t-dsp/t-dsp_tac5212_pro_audio_module/3d_models/SK6812.step

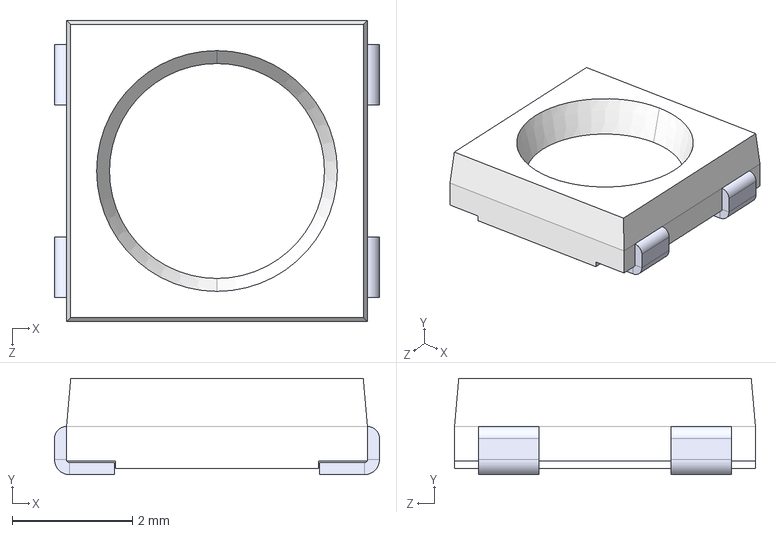
[picture p26: CAD file, 2025-04-21]
3d_models/SK6812.step
5.40 x 1.60 x 5.00 mm
