t-dsp/t-dsp_tac5212_pro_audio_module/3d_models/Same_Sky_SJ3-35083D-TR.step

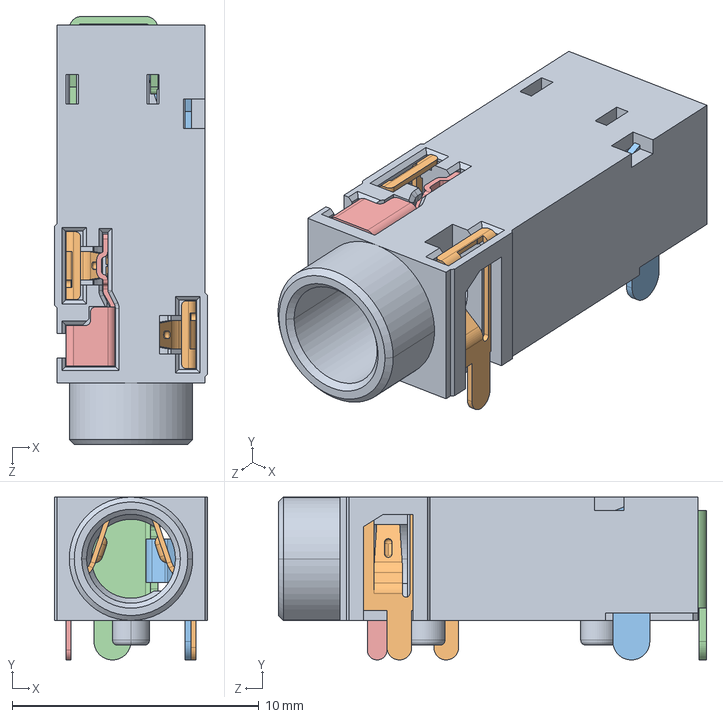
[picture p27: CAD file, 2025-04-21]
3d_models/Same_Sky_SJ3-35083D-TR.step
6.20 x 6.60 x 17.3 mm
