t-dsp/t-dsp_tac5212_pro_audio_module/3d_models/PEC12R-2220F-S0024.step

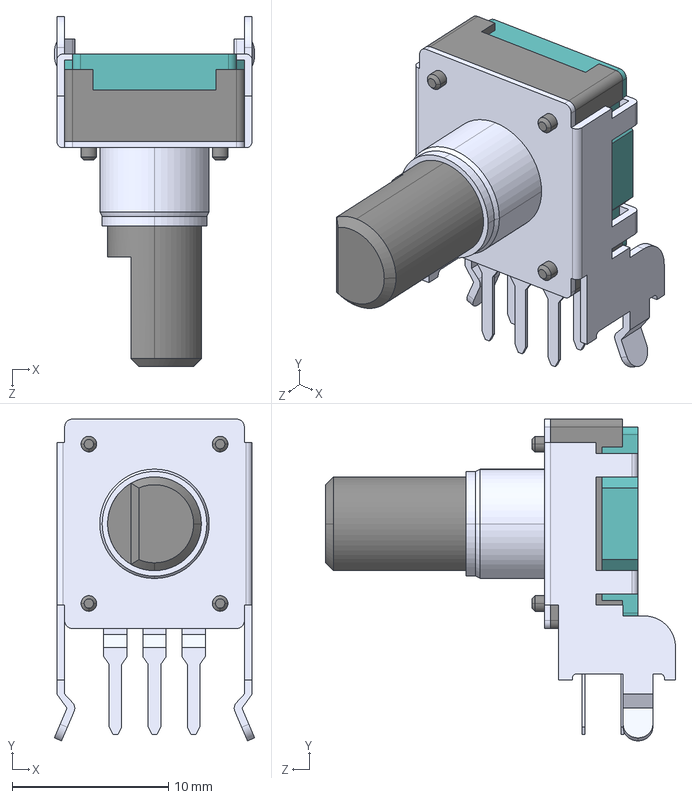
[picture p29: CAD file, 2025-04-21]
3d_models/PEC12R-2220F-S0024.step
12.8 x 20.6 x 22.4 mm
