t-dsp/t-dsp_tac5212_pro_audio_module/3d_models/Tactile_Switch_4.54.5MM.stp

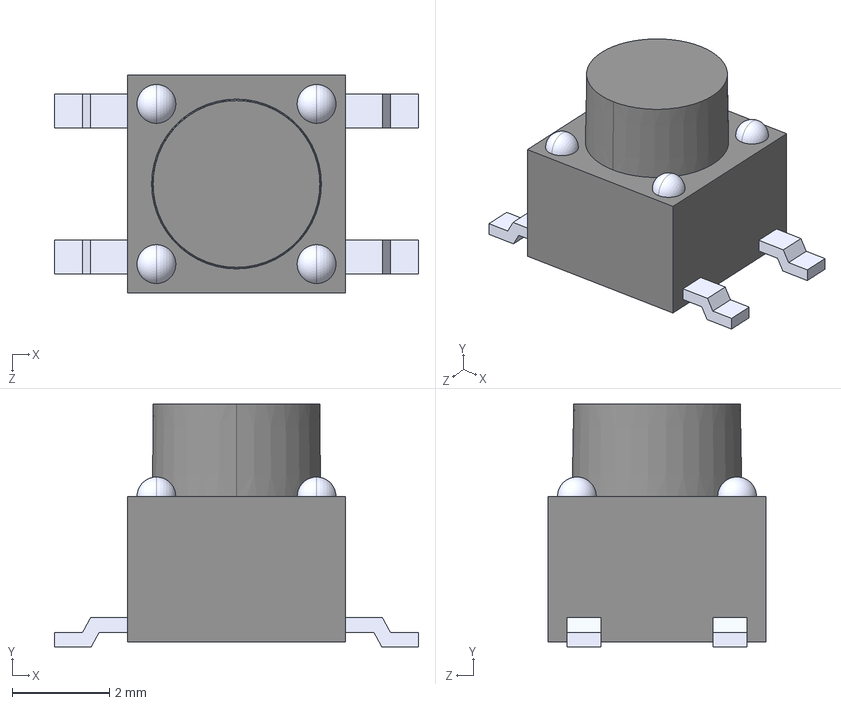
[picture p30: CAD file, 2025-04-21]
3d_models/Tactile_Switch_4.54.5MM.stp
7.50 x 5.00 x 4.50 mm
