t-dsp/t-dsp_tac5212_pro_audio_module/3d_models/JST - XH - Thru (V) - 2Pin - 2.54mm.stp

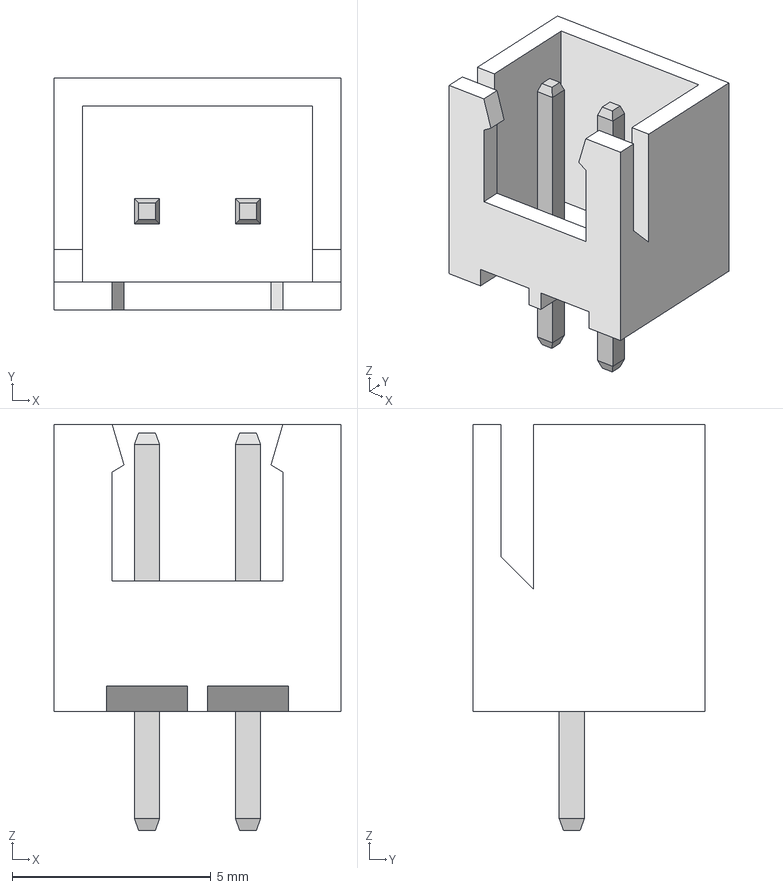
[picture p32: CAD file, 2024-03-24]
3d_models/JST - XH - Thru (V) - 2Pin - 2.54mm.stp
7.21 x 5.84 x 10.2 mm
