t-dsp/t-dsp_tac5212_pro_audio_module/3d_models/4691.step

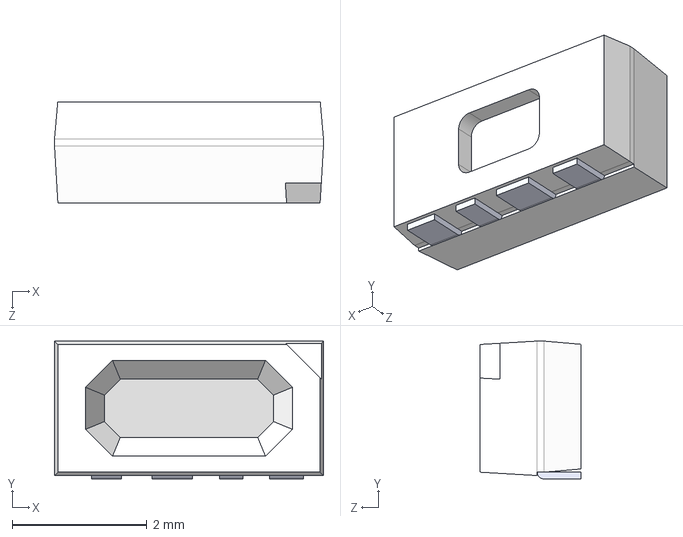
[picture p33: CAD file, 2024-03-24]
3d_models/4691.step
4.00 x 2.05 x 1.50 mm
