t-dsp/t-dsp_tac5212_pro_audio_module/3d_models/1808--3DModel-STEP-630548.STEP

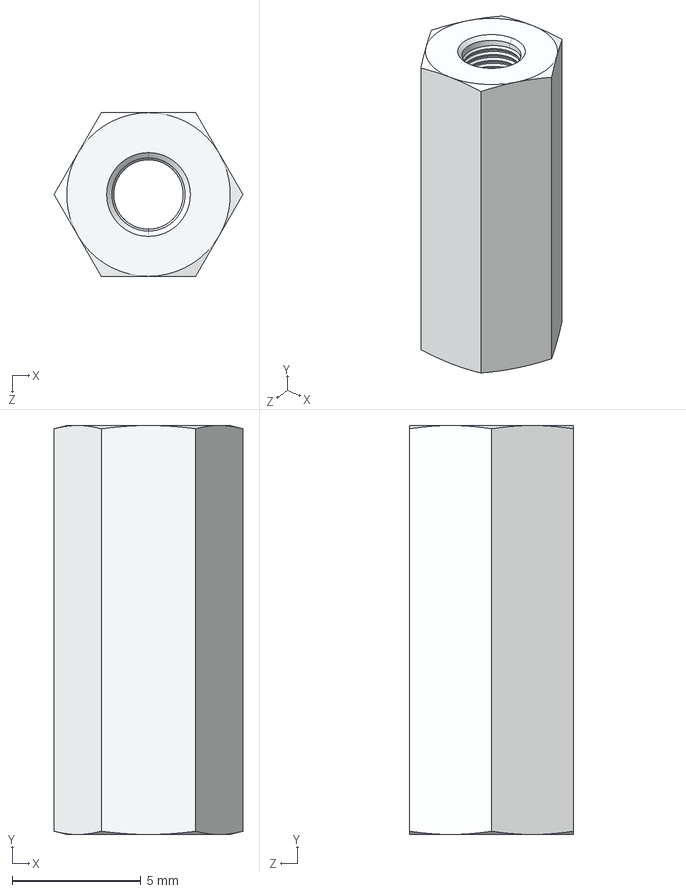
[picture p36: CAD file, 2024-03-16]
3d_models/1808--3DModel-STEP-630548.STEP
7.33 x 15.9 x 6.35 mm
