t-dsp/t-dsp_tac5212_pro_audio_module/3d_models/c-6364372-2-o-3d.stp

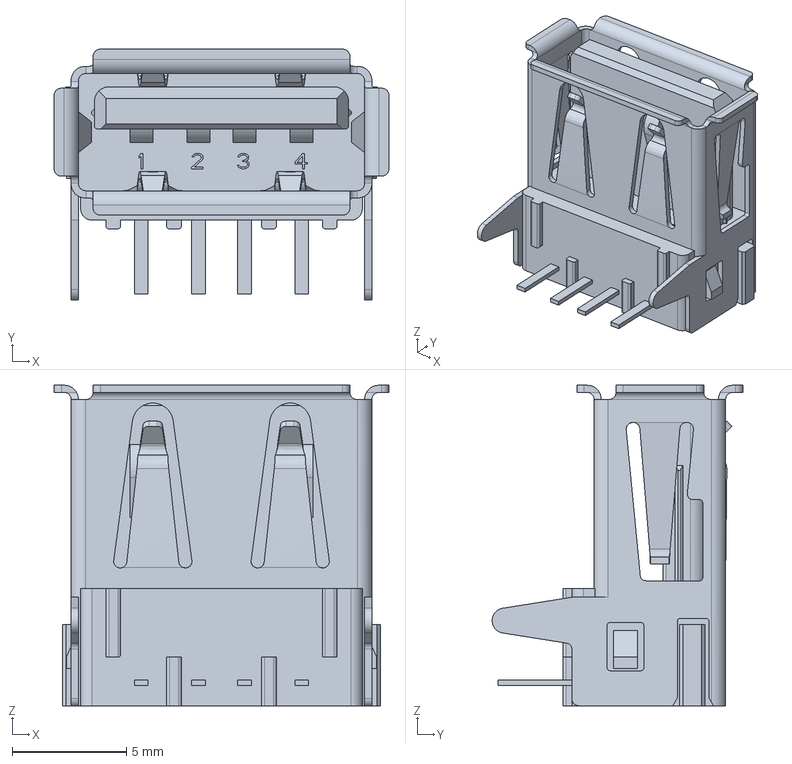
[picture p37: CAD file, 2024-02-26]
3d_models/c-6364372-2-o-3d.stp
14.6 x 10.9 x 14.0 mm
