t-dsp/t-dsp_tac5212_pro_audio_module/3d_models/Bracket 4-40 621.STEP

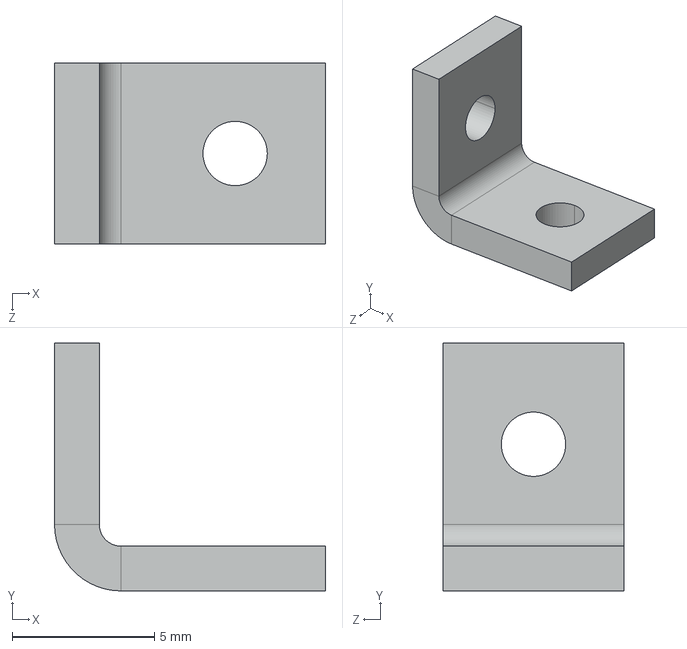
[picture p38: CAD file, 2024-02-26]
3d_models/Bracket 4-40 621.STEP
9.53 x 8.71 x 6.35 mm
