t-dsp/t-dsp_tac5212_pro_audio_module/3d_models/MicroFit3-43045-0428.stp

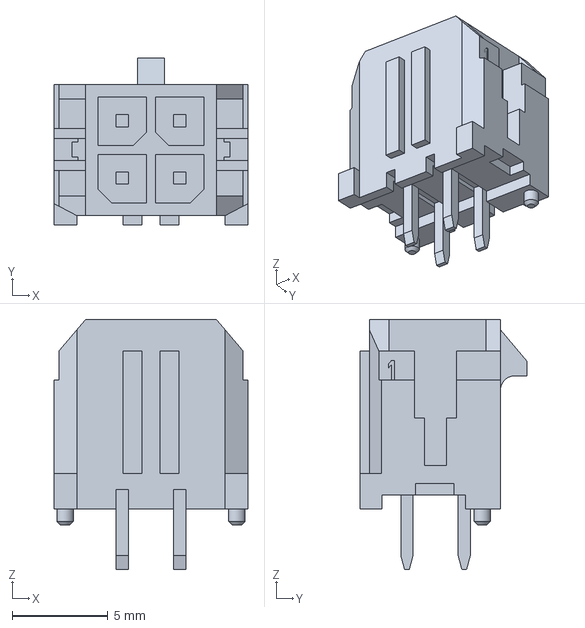
[picture p39: CAD file, 2024-02-26]
3d_models/MicroFit3-43045-0428.stp
10.1 x 8.77 x 13.1 mm
