t-dsp/t-dsp_tac5212_pro_audio_module/3d_models/3-D NC3MAH.stp

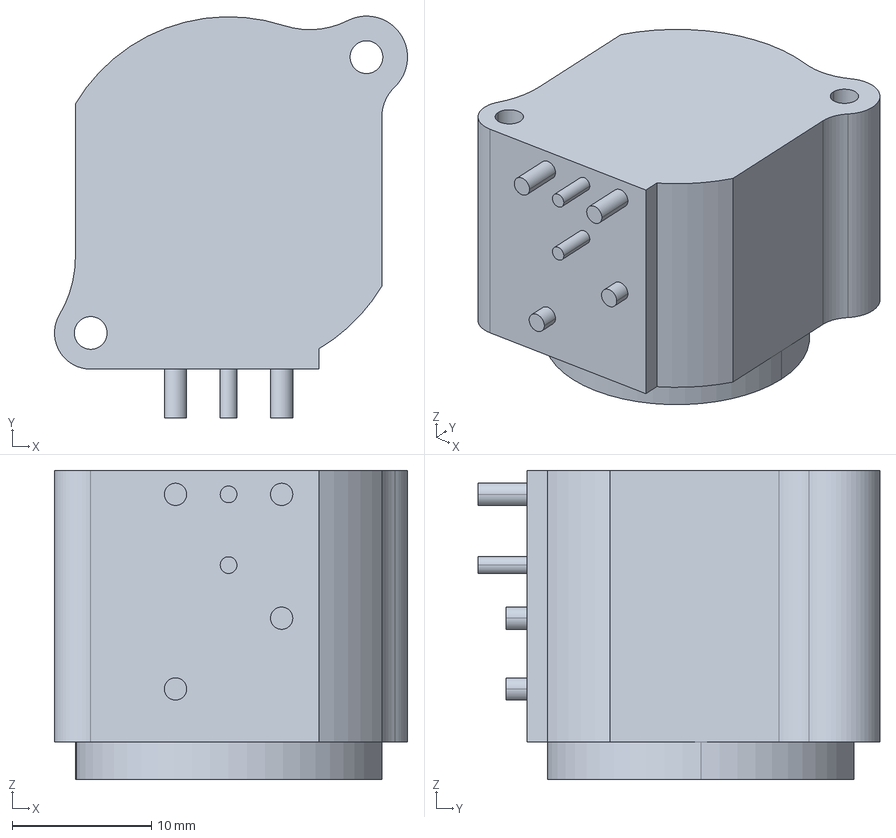
[picture p40: CAD file, 2024-02-26]
3d_models/3-D NC3MAH.stp
25.3 x 28.8 x 22.2 mm
