t-dsp/t-dsp_tac5212_pro_audio_module/3d_models/PinHeader_1x02_P2.54mm_Vertical.step

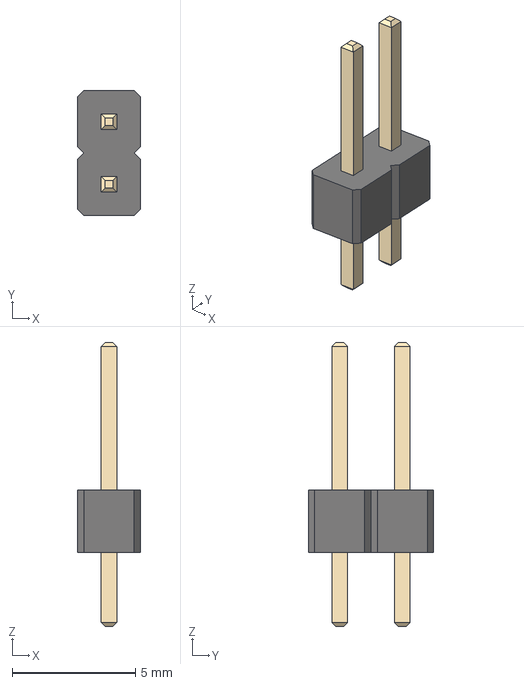
[picture p41: CAD file, 2024-02-26]
3d_models/PinHeader_1x02_P2.54mm_Vertical.step
2.54 x 5.08 x 11.5 mm
