t-dsp/t-dsp_tac5212_pro_audio_module/3d_models/74LS00.step

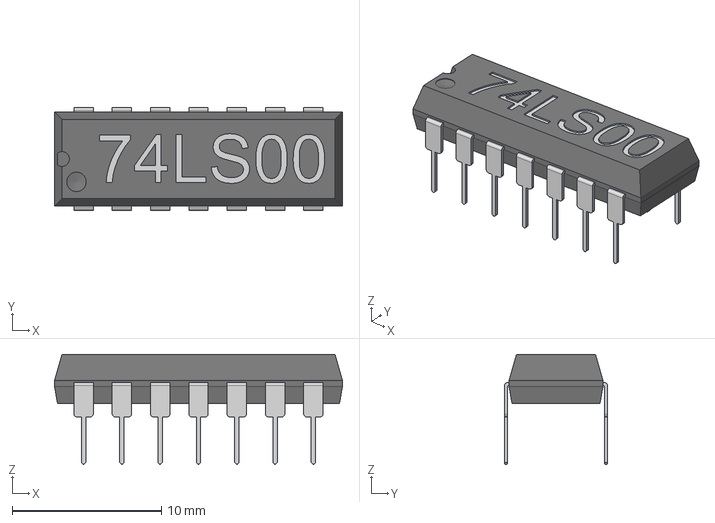
[picture p42: CAD file, 2024-02-26]
3d_models/74LS00.step
19.3 x 6.90 x 7.40 mm
