t-dsp/t-dsp_tac5212_pro_audio_module/3d_models/COMBO_XLR_NCJ6FI-H-0.stp

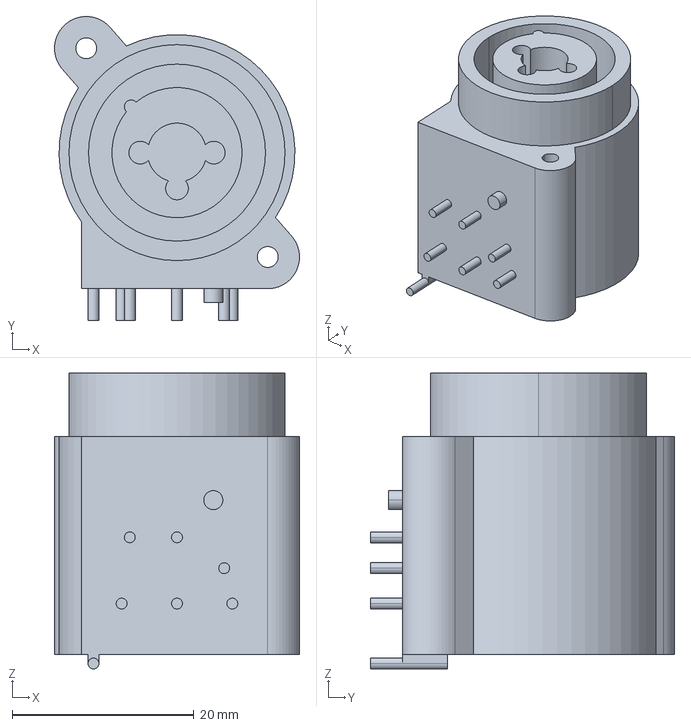
[picture p44: CAD file, 2024-02-26]
3d_models/COMBO_XLR_NCJ6FI-H-0.stp
27.0 x 33.5 x 32.6 mm
