t-dsp/t-dsp_tac5212_pro_audio_module/3d_models/COMBO-NCJ6FA-H.step

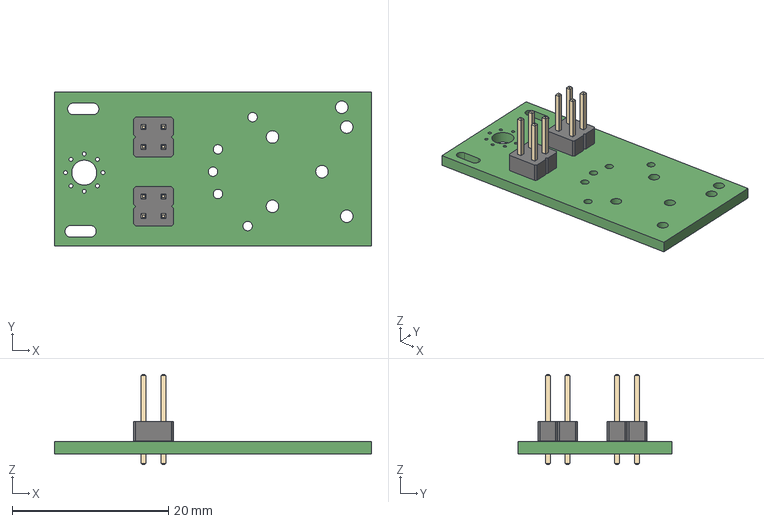
[picture p45: CAD file, 2024-02-26]
3d_models/COMBO-NCJ6FA-H.step
40.6 x 19.7 x 11.5 mm
