t-dsp/t-dsp_tac5212_pro_audio_module/3d_models/35RAPC7JS_SIMPLIFIED.step

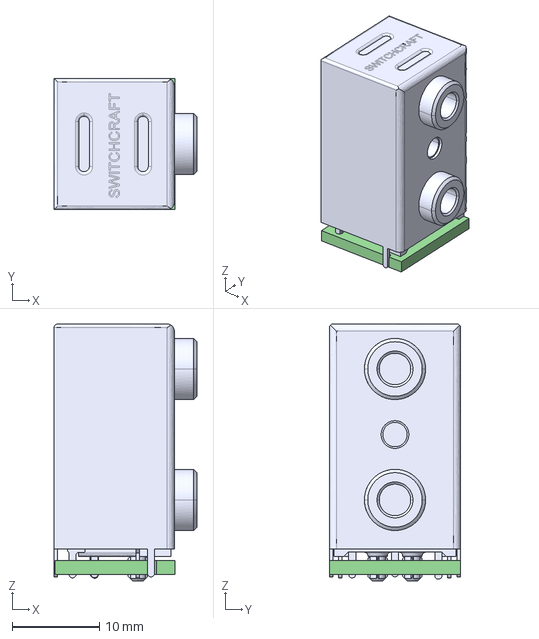
[picture p46: CAD file, 2024-02-26]
3d_models/35RAPC7JS_SIMPLIFIED.step
16.4 x 15.0 x 29.5 mm
IO_3.5_35RAPC7JS PCB
