t-dsp/t-dsp_tac5212_pro_audio_module/3d_models/pjras1x2s_Series.STEP

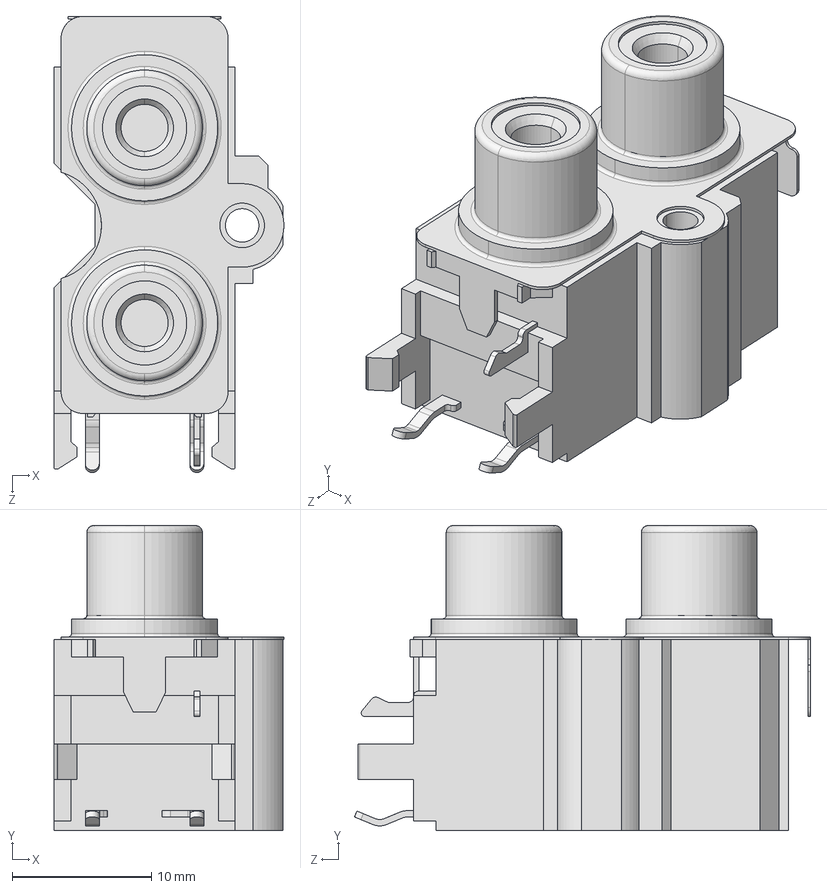
[picture p47: CAD file, 2024-02-26]
3d_models/pjras1x2s_Series.STEP
16.5 x 21.9 x 32.7 mm
