t-dsp/t-dsp_tac5212_pro_audio_module/3d_models/SD_CARD_DM3D-SF.step

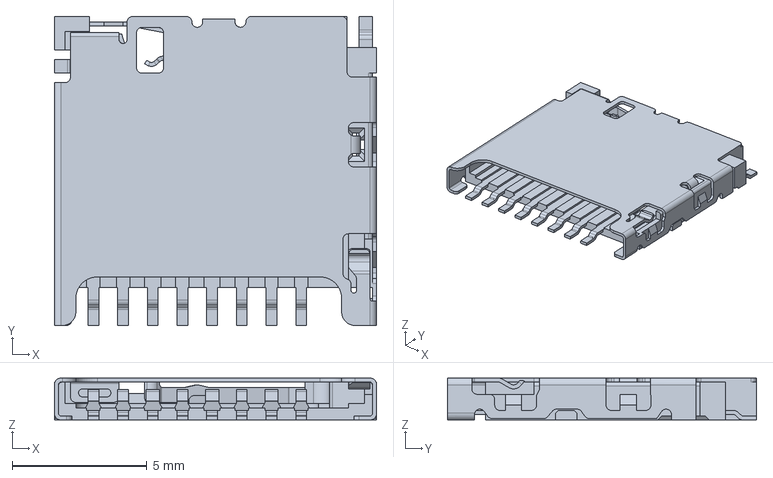
[picture p48: CAD file, 2024-02-26]
3d_models/SD_CARD_DM3D-SF.step
11.9 x 11.4 x 1.55 mm
