t-dsp/t-dsp_tac5212_pro_audio_module/3d_models/c-292304-1-b-3d.stp

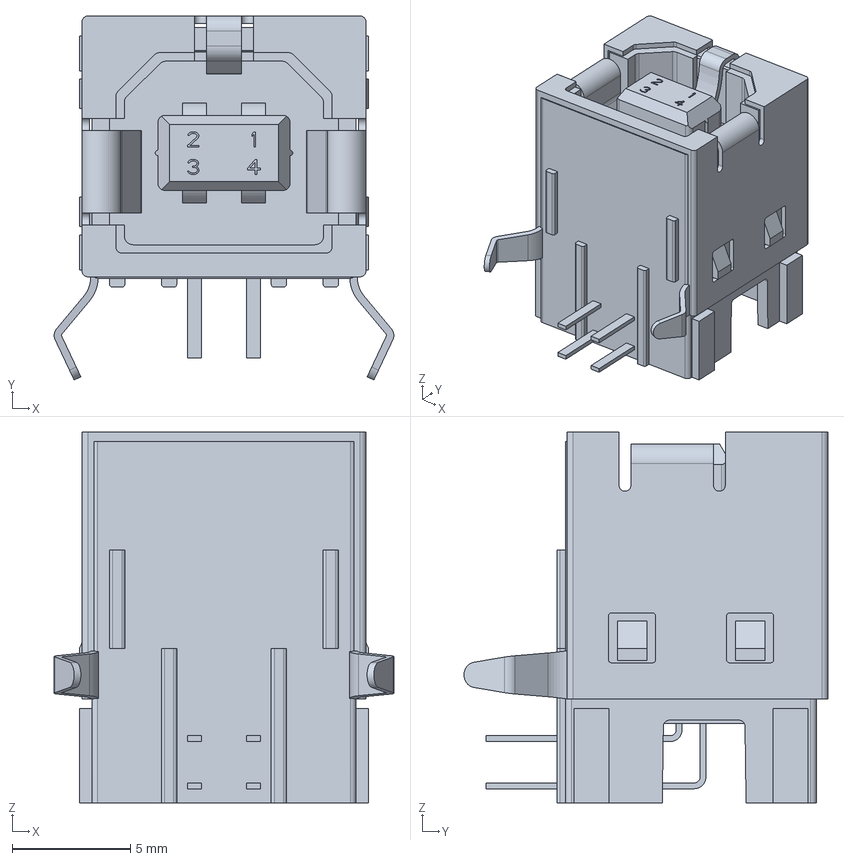
[picture p49: CAD file, 2024-02-26]
3d_models/c-292304-1-b-3d.stp
14.4 x 15.4 x 15.7 mm
