t-dsp/t-dsp_tac5212_pro_audio_module/3d_models/TOSLINK_3D_MODEL_PLT133_T9.step

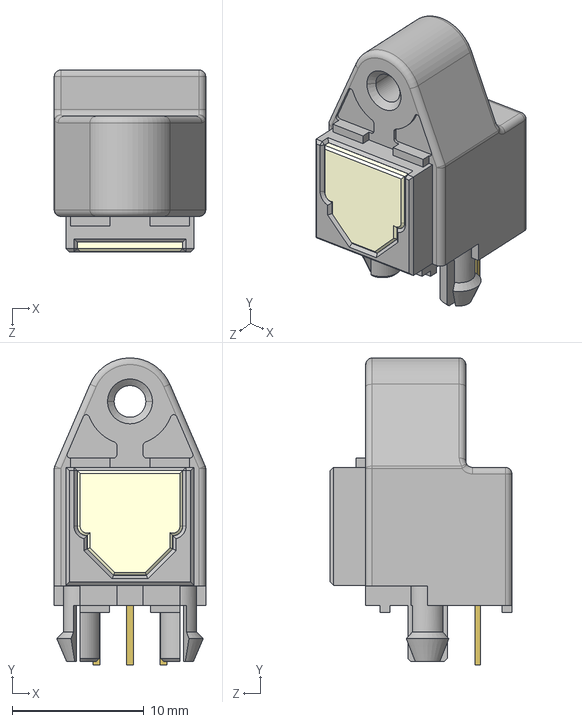
[picture p51: CAD file, 2024-02-26]
3d_models/TOSLINK_3D_MODEL_PLT133_T9.step
11.5 x 23.3 x 13.8 mm
