t-dsp/t-dsp_tac5212_pro_audio_module/3d_models/3.5MM_STEREO_35RAPC4BHN2.STEP

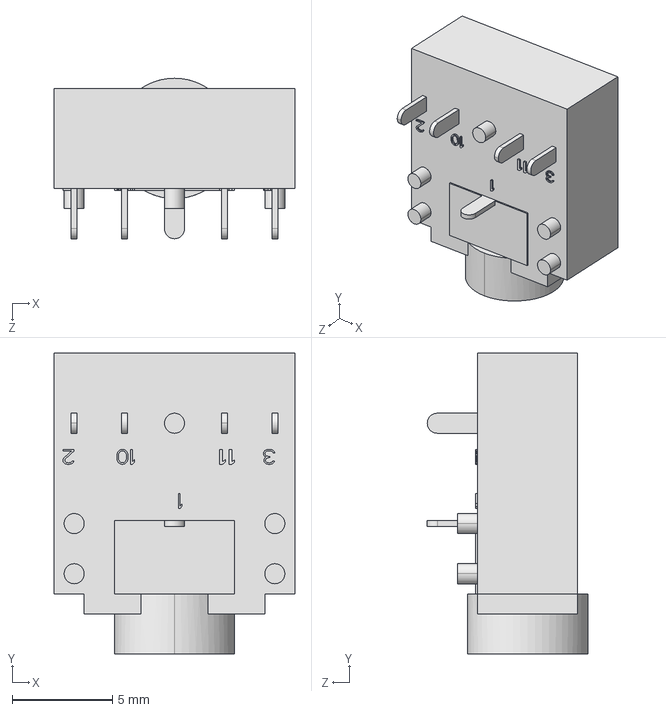
[picture p52: CAD file, 2024-02-26]
3d_models/3.5MM_STEREO_35RAPC4BHN2.STEP
12.0 x 15.0 x 8.00 mm
