t-dsp/t-dsp_tac5212_pro_audio_module/3d_models/SPDIF_pjran1x1_Series.STEP

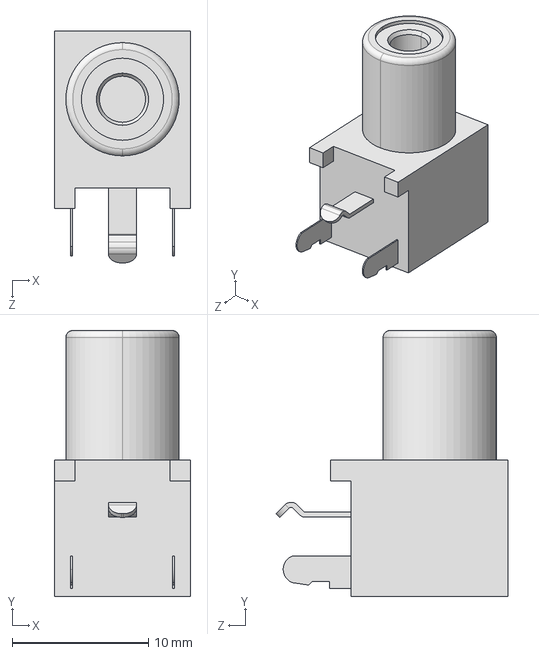
[picture p53: CAD file, 2024-02-26]
3d_models/SPDIF_pjran1x1_Series.STEP
10.00 x 19.5 x 17.0 mm
