t-dsp/t-dsp_tac5212_pro_audio_module/3d_models/USB-B1HS - USB-B1H Interconnect USB Type B.stp

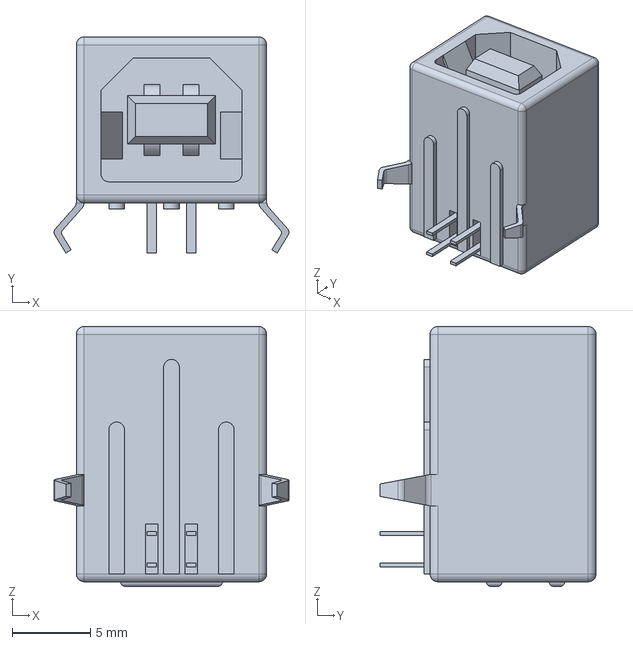
[picture p54: CAD file, 2024-02-26]
3d_models/USB-B1HS - USB-B1H Interconnect USB Type B.stp
15.0 x 13.8 x 16.6 mm
