t-dsp/t-dsp_tac5212_pro_audio_module/3d_models/USB_A_c-292303-4-f-3d.stp

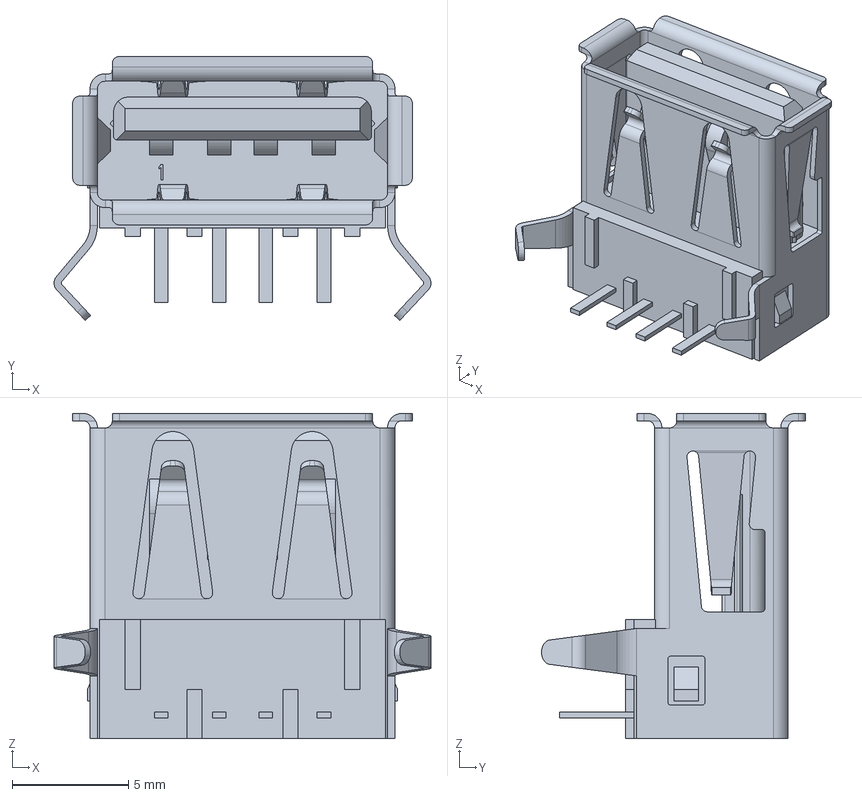
[picture p55: CAD file, 2024-02-26]
3d_models/USB_A_c-292303-4-f-3d.stp
16.2 x 11.4 x 14.0 mm
