t-dsp/t-dsp_tac5212_pro_audio_module/3d_models/SOIC-14_3.9x8.7mm_P1.27mm.step

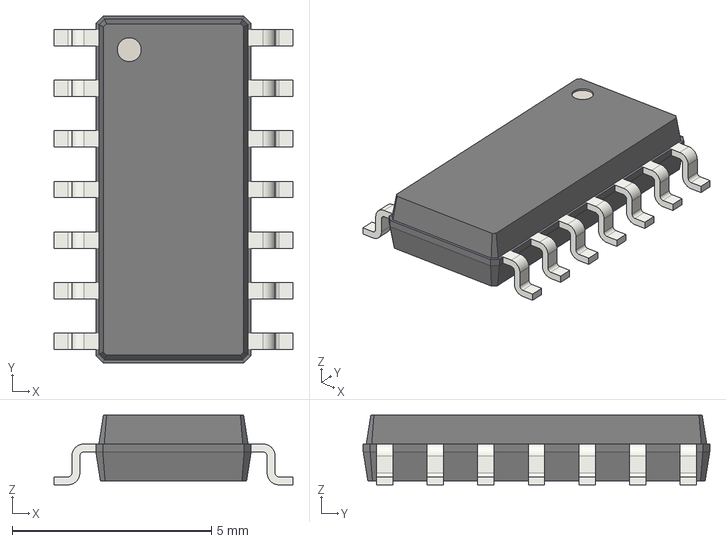
[picture p57: CAD file, 2024-02-26]
3d_models/SOIC-14_3.9x8.7mm_P1.27mm.step
6.00 x 8.70 x 1.75 mm
