t-dsp/t-dsp_tac5212_pro_audio_module/3d_models/SOIC-14W_7.5x9.0mm_P1.27mm.step

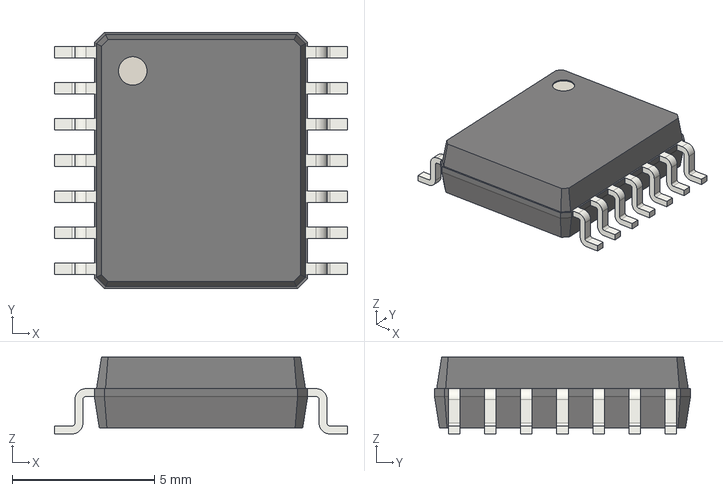
[picture p58: CAD file, 2024-02-26]
3d_models/SOIC-14W_7.5x9.0mm_P1.27mm.step
10.3 x 9.00 x 2.70 mm
