t-dsp/t-dsp_tac5212_pro_audio_module/3d_models/pjras2x2s_Series.STEP

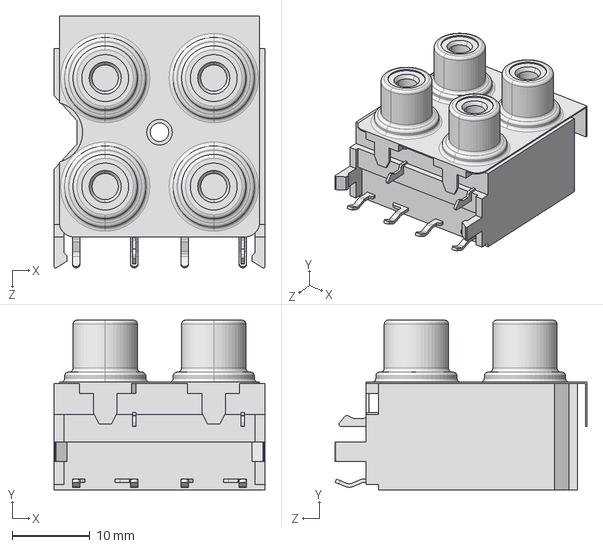
[picture p59: CAD file, 2024-02-26]
3d_models/pjras2x2s_Series.STEP
27.2 x 21.9 x 32.5 mm
