t-dsp/t-dsp_tac5212_pro_audio_module/3d_models/DC_BARREL_PJ-202AH.step

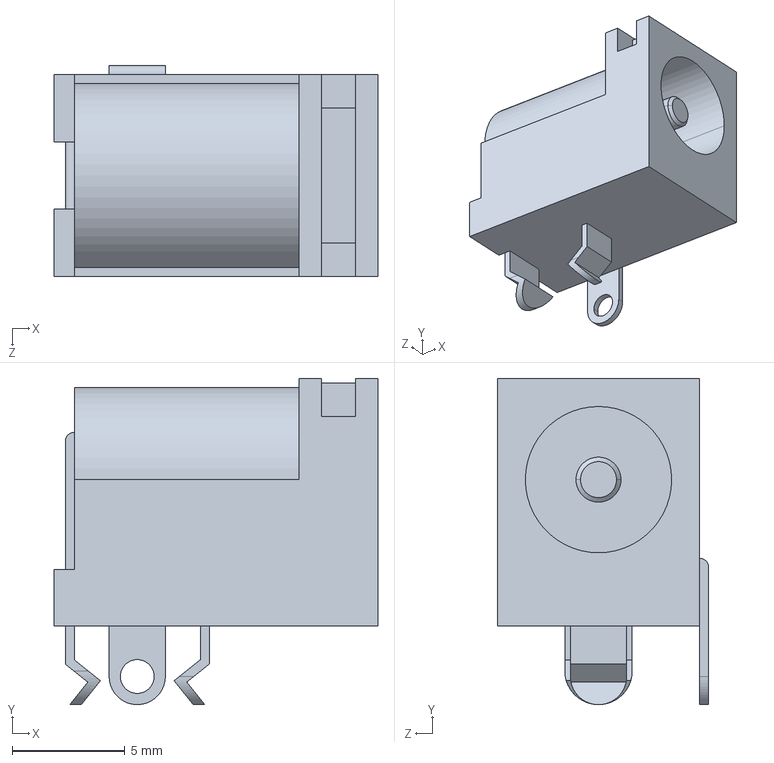
[picture p60: CAD file, 2024-02-26]
3d_models/DC_BARREL_PJ-202AH.step
14.4 x 14.5 x 9.40 mm
