t-dsp/t-dsp_tac5212_pro_audio_module/3d_models/J1B1211CCD.STEP

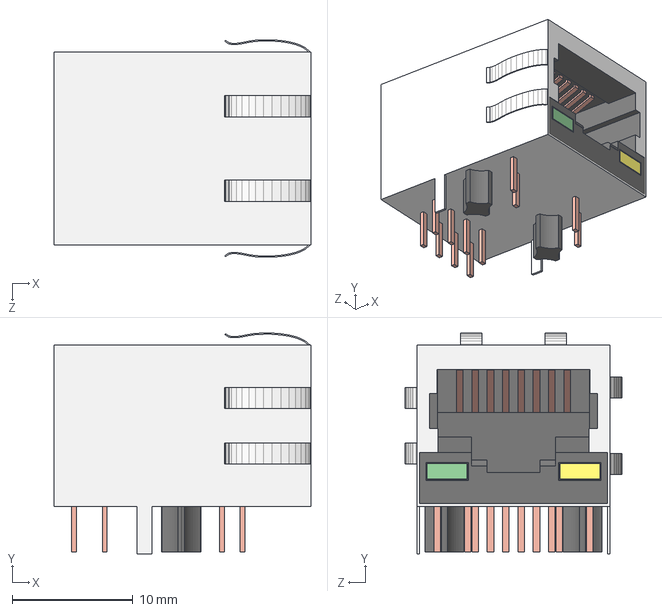
[picture p61: CAD file, 2024-02-26]
3d_models/J1B1211CCD.STEP
21.3 x 18.3 x 18.0 mm
