t-dsp/t-dsp_tac5212_pro_audio_module/3d_models/35RAPC3BH3.STEP

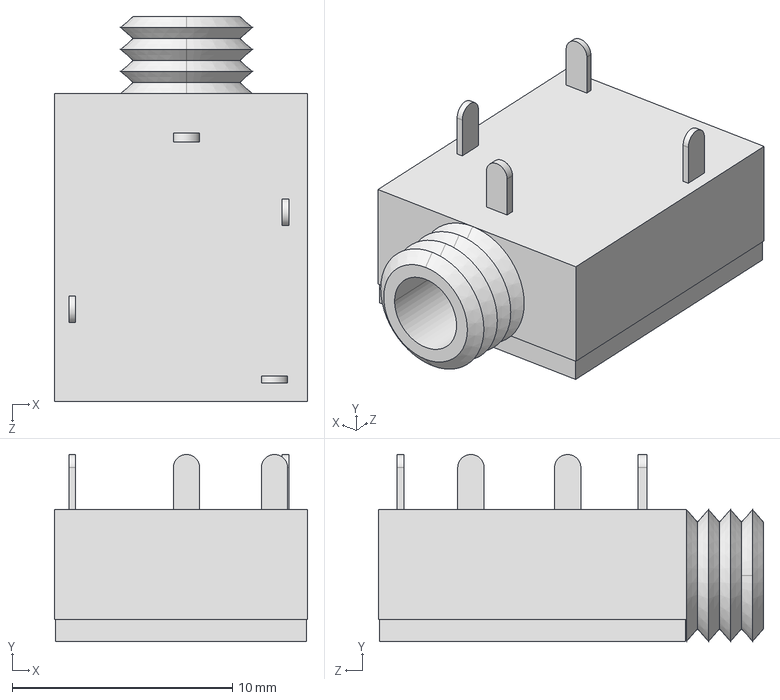
[picture p62: CAD file, 2024-02-26]
3d_models/35RAPC3BH3.STEP
11.5 x 8.50 x 17.5 mm
