t-dsp/t-dsp_tac5212_pro_audio_module/3d_models/35RAPC7JS.STEP

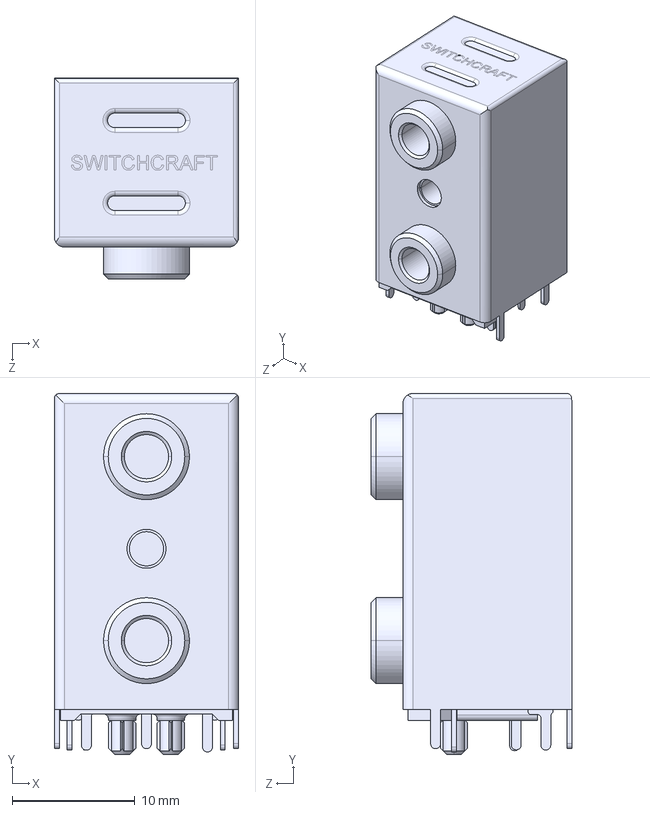
[picture p64: CAD file, 2024-02-26]
3d_models/35RAPC7JS.STEP
15.0 x 29.5 x 16.4 mm
